bitaxeorg/BitaxeGT/3d/DISST7789-176x320.STEP

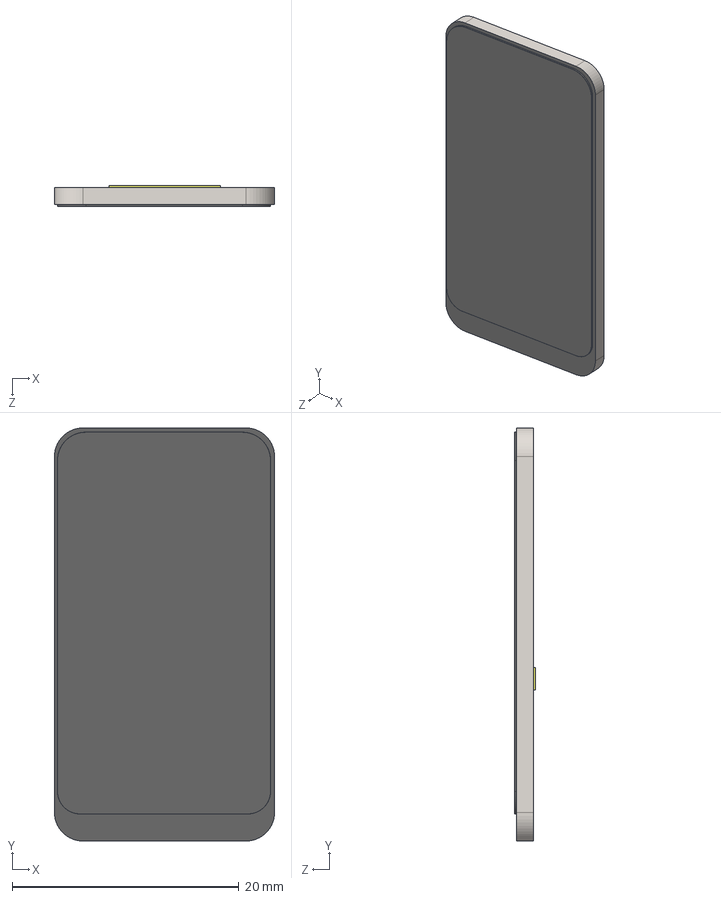
[picture p16: CAD file, 2024-10-16]
3d/DISST7789-176x320.STEP
19.4 x 36.4 x 1.86 mm
