bitaxeorg/BitaxeGT/3d/TPS546D24ARVFR.step

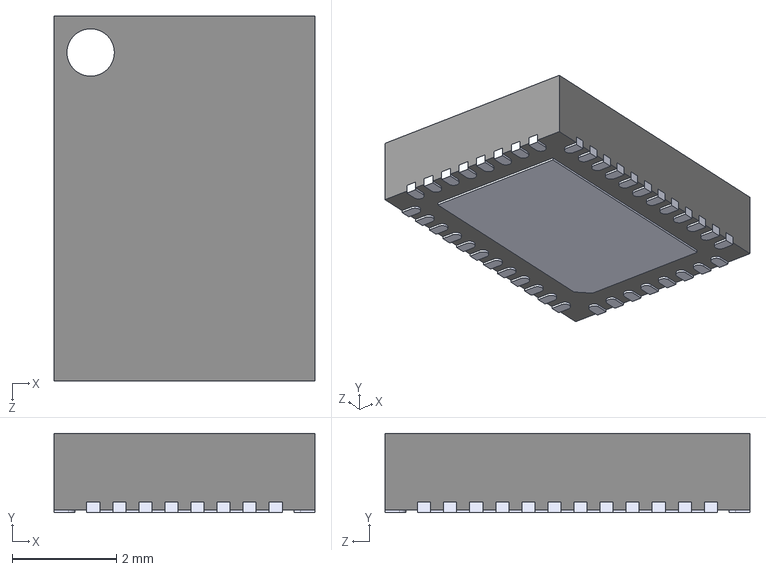
[picture p19: CAD file, 2024-10-16]
3d/TPS546D24ARVFR.step
5.00 x 1.52 x 7.00 mm
