bitaxeorg/BitaxeGT/3d/BM1368xx.stp

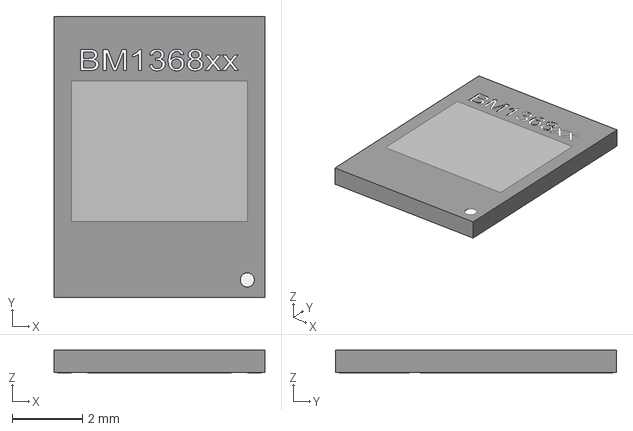
[picture p20: CAD file, 2024-10-16]
3d/BM1368xx.stp
6.00 x 8.00 x 0.65 mm
