bitaxeorg/BitaxeGT/3d/CUI_DEVICES_PJ-036AH-SMT-TR.step

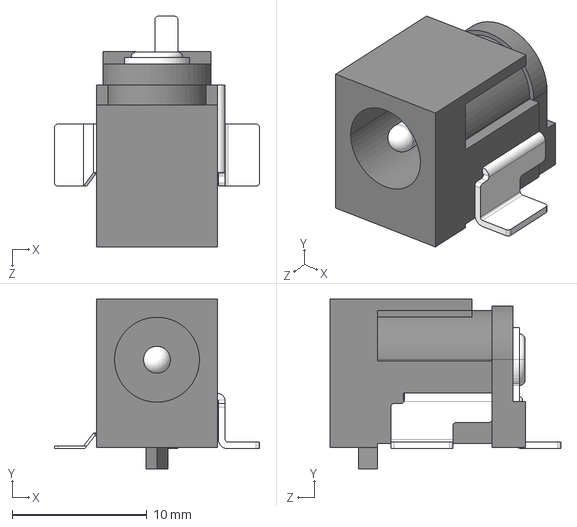
[picture p21: CAD file, 2024-10-16]
3d/CUI_DEVICES_PJ-036AH-SMT-TR.step
15.2 x 12.6 x 17.1 mm
