bitaxeorg/BitaxeGT/3d/SLC1175-271MEC_COC.step

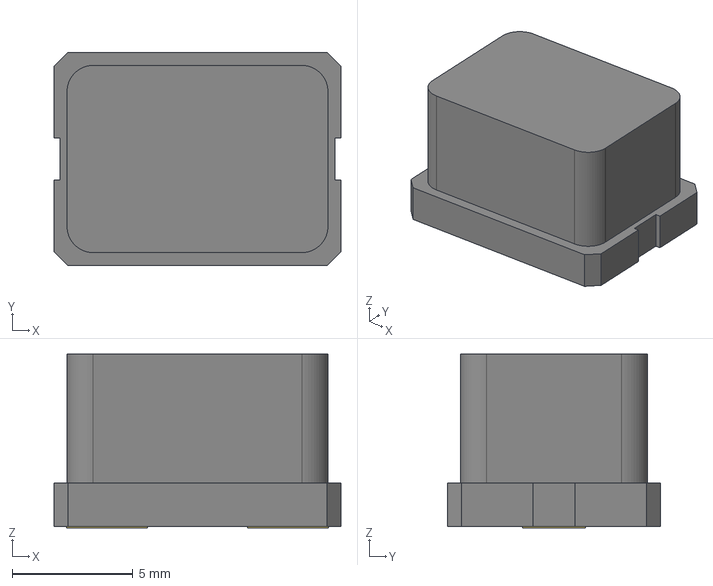
[picture p22: CAD file, 2024-10-16]
3d/SLC1175-271MEC_COC.step
11.9 x 8.83 x 7.19 mm
