bitaxeorg/BitaxeGT/3d/USB_10118193-0001LF.STEP

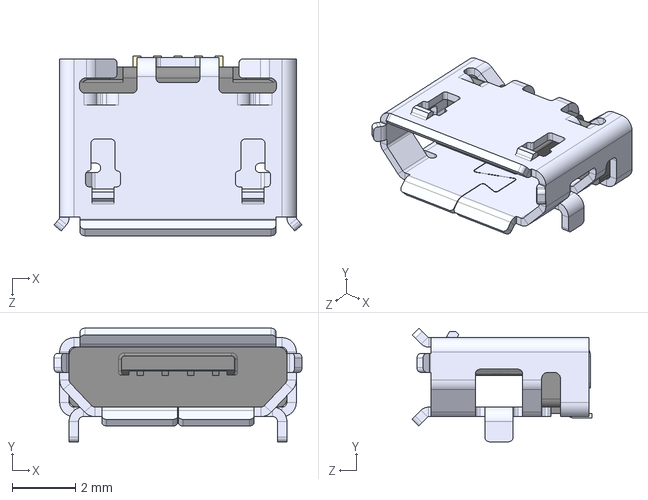
[picture p23: CAD file, 2024-10-16]
3d/USB_10118193-0001LF.STEP
7.86 x 3.60 x 5.71 mm
