bitaxeorg/BitaxeGT/3d/IHLP2020CZ.step

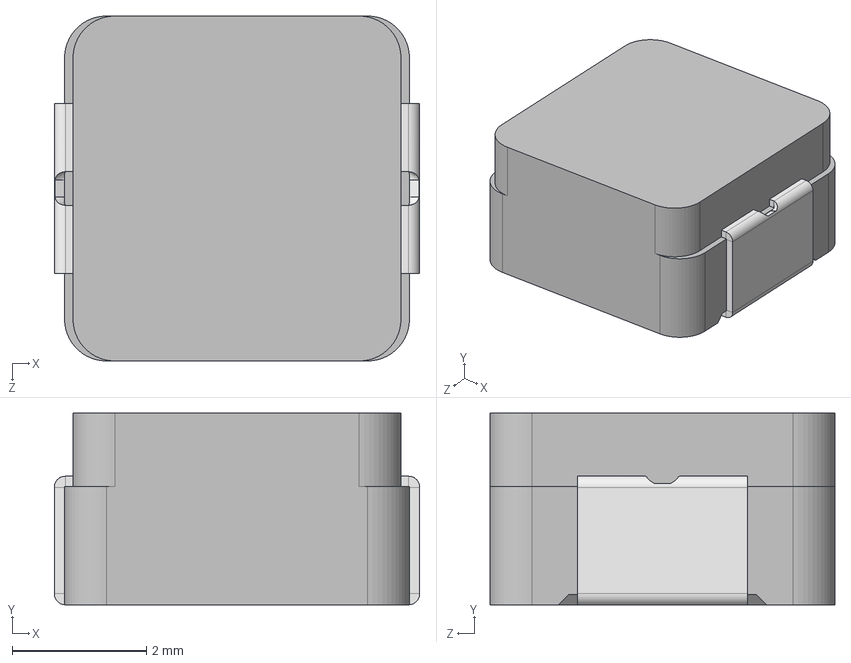
[picture p24: CAD file, 2024-10-16]
3d/IHLP2020CZ.step
5.45 x 2.86 x 5.15 mm
