bitaxeorg/BitaxeGT/3d/TSOT-23-5_RIT.step

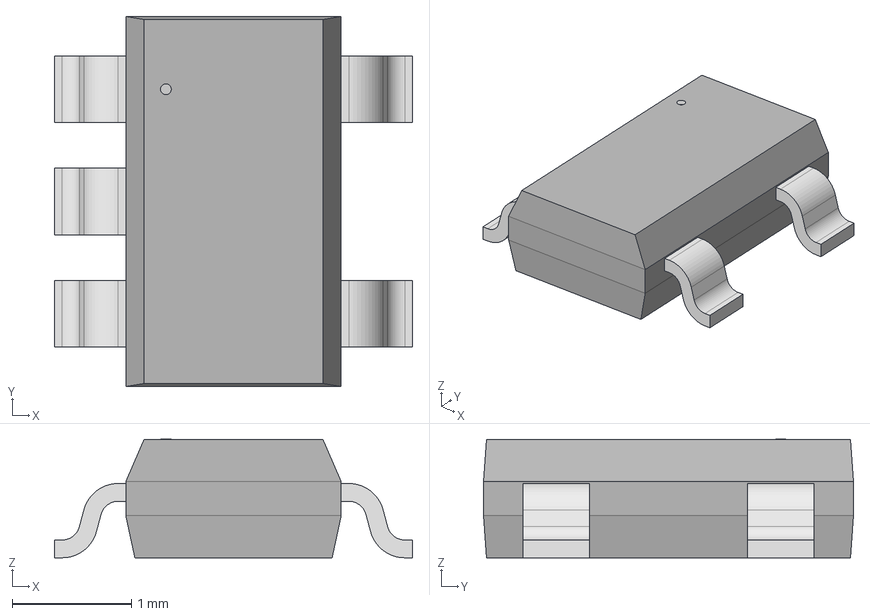
[picture p25: CAD file, 2024-10-16]
3d/TSOT-23-5_RIT.step
3.00 x 3.10 x 0.993 mm
