bitaxeorg/BitaxeGT/3d/DRC0010J.stp

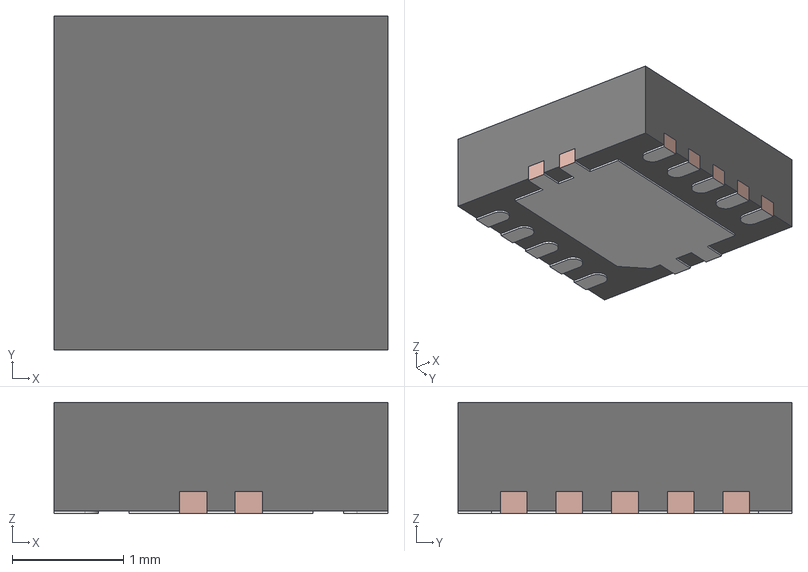
[picture p26: CAD file, 2024-10-16]
3d/DRC0010J.stp
3.00 x 3.00 x 1.00 mm
BODY-SON
FRAME-DRC0010J
