bitaxeorg/BitaxeGT/3d/SOT-23-5_M5_MCH.step

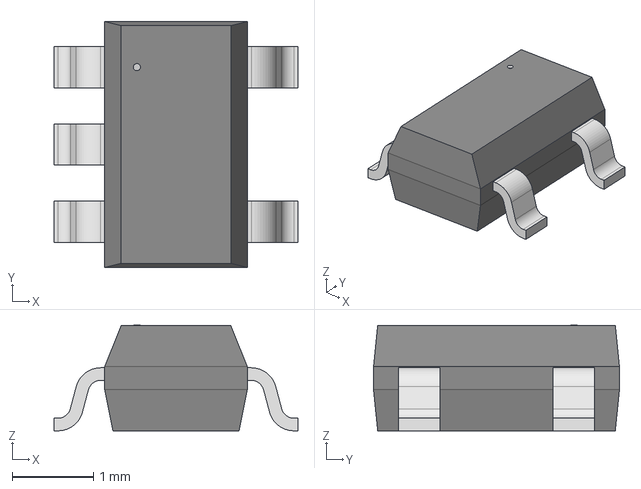
[picture p29: CAD file, 2024-10-16]
3d/SOT-23-5_M5_MCH.step
3.00 x 3.02 x 1.30 mm
