bitaxeorg/BitaxeGT/3d/Bitaxe_Heatsink.step

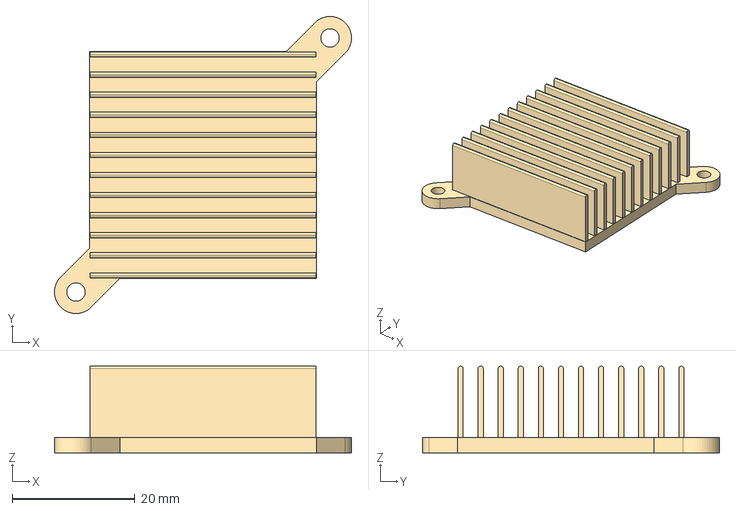
[picture p31: CAD file, 2024-10-16]
3d/Bitaxe_Heatsink.step
48.4 x 48.4 x 14.1 mm
