bitaxeorg/BitaxeGT/3d/oscillator3.2x2.5.step

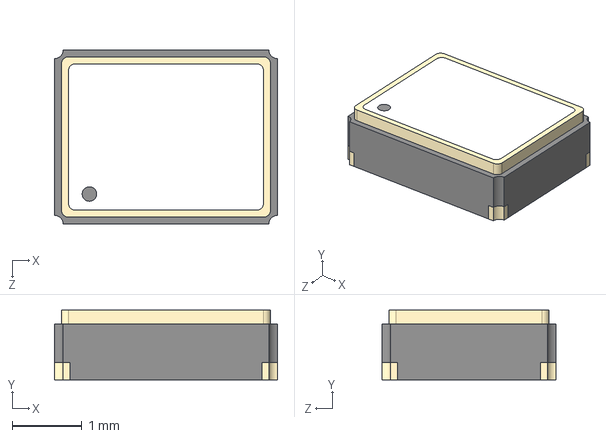
[picture p32: CAD file, 2024-10-16]
3d/oscillator3.2x2.5.step
3.20 x 1.00 x 2.50 mm
