bitaxeorg/BitaxeGT/3d/CS1213AG-tr.stp

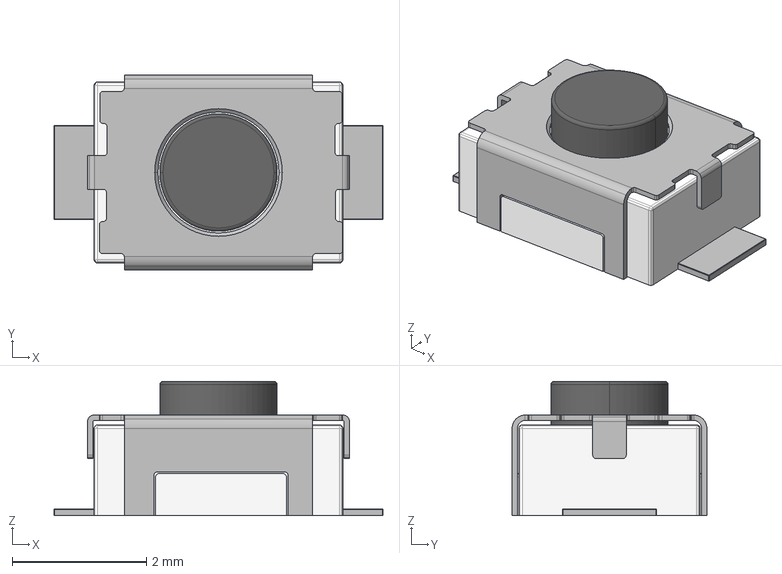
[picture p35: CAD file, 2024-10-16]
3d/CS1213AG-tr.stp
4.90 x 2.90 x 2.00 mm
