bitaxeorg/BitaxeGT/3d/CX3225SB16000H0FLJCC.STEP

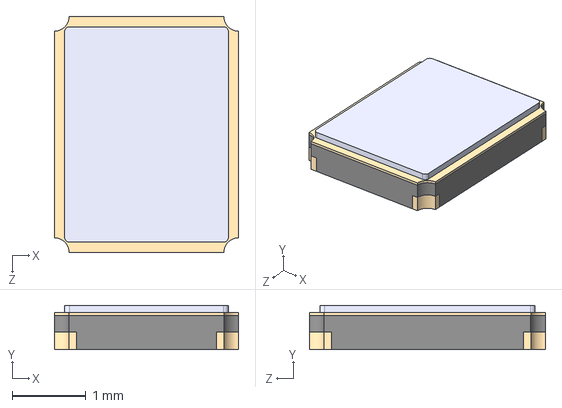
[picture p37: CAD file, 2024-10-16]
3d/CX3225SB16000H0FLJCC.STEP
2.50 x 0.6 x 3.20 mm
