bitaxeorg/BitaxeGT/3d/CUI_DEVICES_PJ-002AH.step

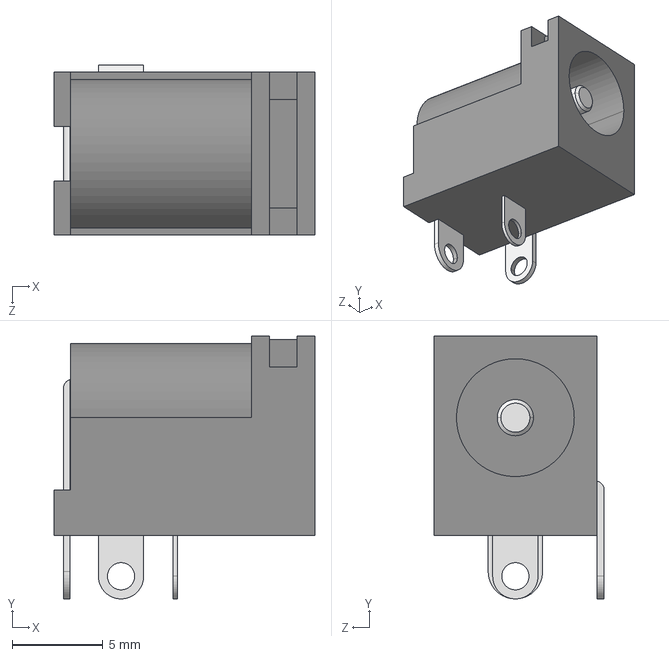
[picture p43: CAD file, 2024-10-16]
3d/CUI_DEVICES_PJ-002AH.step
14.4 x 14.5 x 9.40 mm
