bitaxeorg/BitaxeGT/3d/CUI_DEVICES_PJ-037AH.step

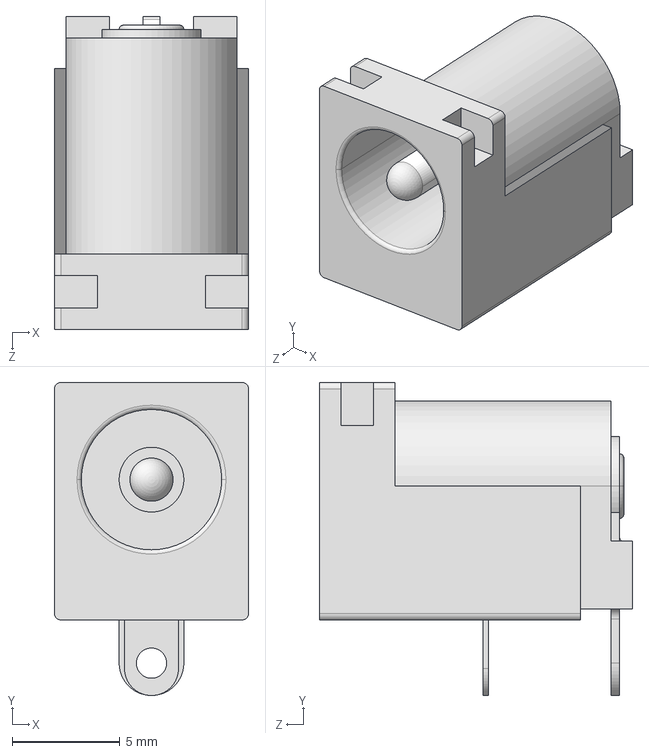
[picture p44: CAD file, 2024-10-16]
3d/CUI_DEVICES_PJ-037AH.step
9.00 x 14.5 x 14.5 mm
