bitaxeorg/BitaxeGT/3d/SMV_z90.stp

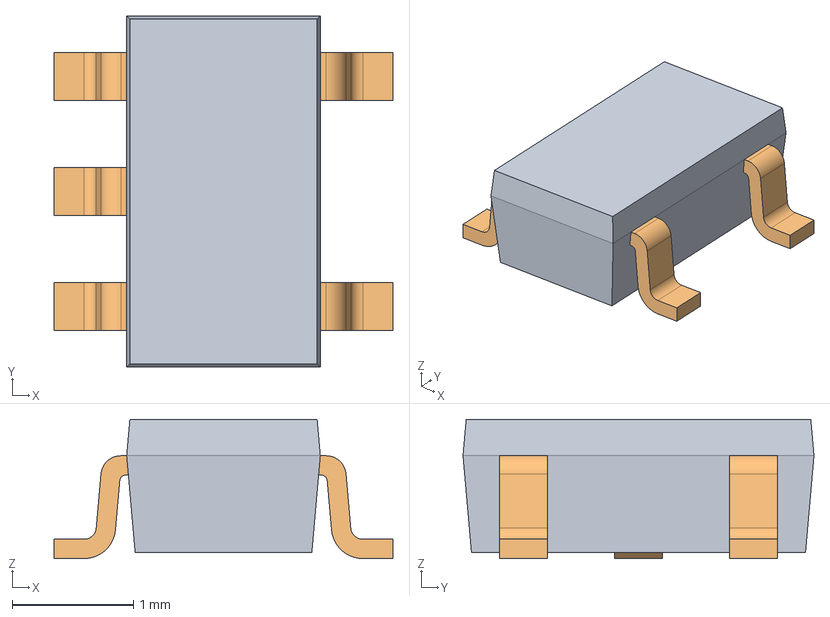
[picture p46: CAD file, 2024-10-16]
3d/SMV_z90.stp
2.80 x 2.90 x 1.15 mm
