bitaxeorg/BitaxeGT/3d/DRL0006A.stp

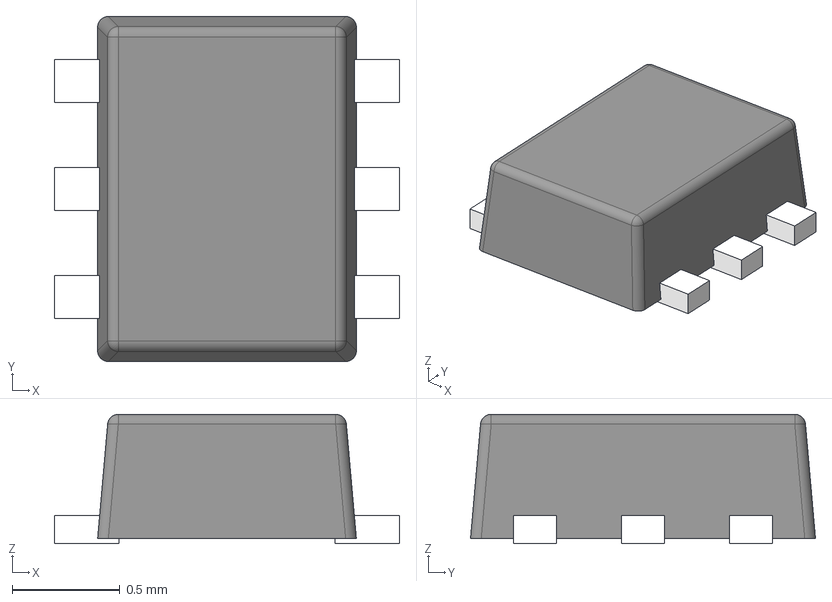
[picture p49: CAD file, 2024-10-16]
3d/DRL0006A.stp
1.60 x 1.60 x 0.6 mm
FRAME-DRL0006A
BODY-SOT
PIN1-ID
