bitaxeorg/BitaxeGT/3d/SW_CS1213AGF260_CRS.step

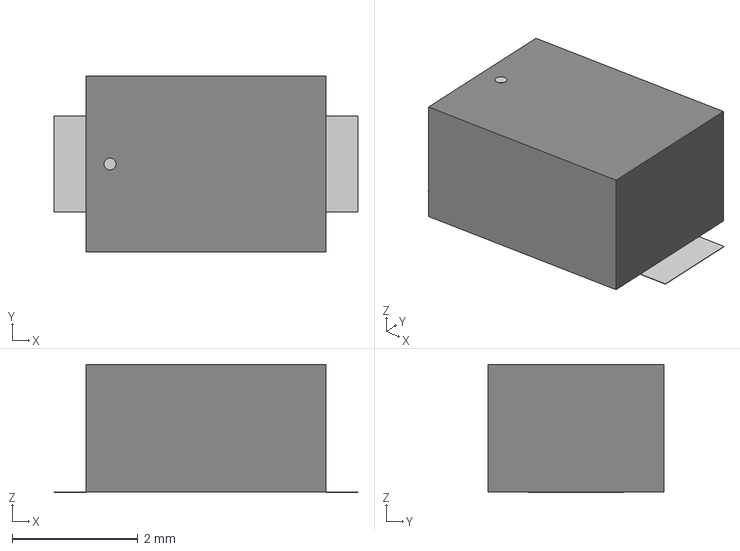
[picture p51: CAD file, 2024-10-16]
3d/SW_CS1213AGF260_CRS.step
4.83 x 2.79 x 2.04 mm
