bitaxeorg/BitaxeGT/3d/Coilcraft-SLC1175.STEP

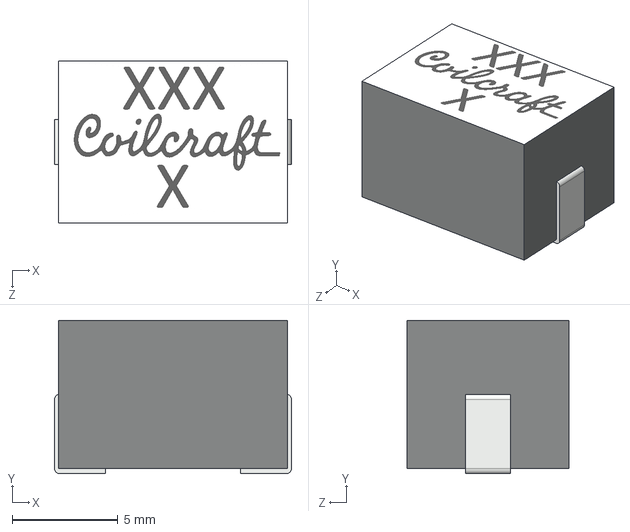
[picture p52: CAD file, 2024-10-16]
3d/Coilcraft-SLC1175.STEP
11.2 x 7.25 x 7.65 mm
